ChrisChrisLoLo/bunchiez40/case/experimental_junk/case.stl

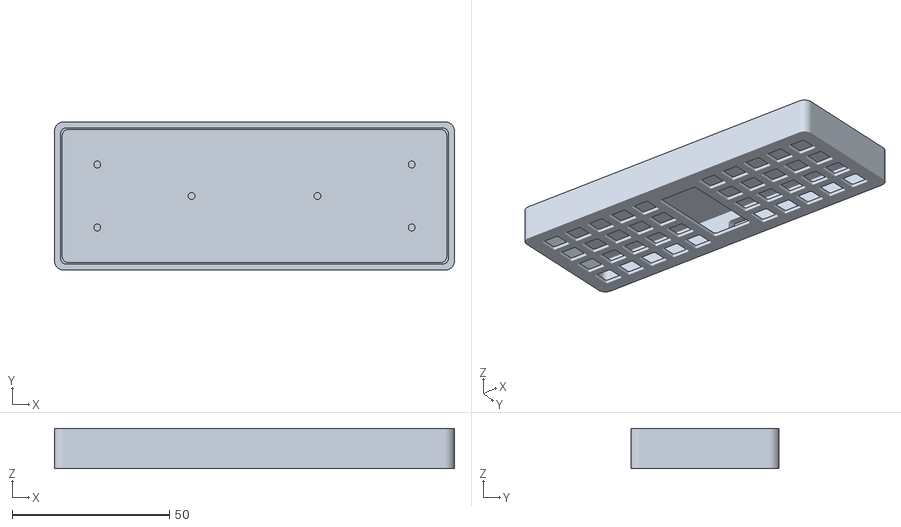
[picture p18: CAD file, 2023-10-13]
case/experimental_junk/case.stl
127.2 x 47.2 x 12.8
