ChrisChrisLoLo/bunchiez40/case/experimental_junk/keycaps.stl

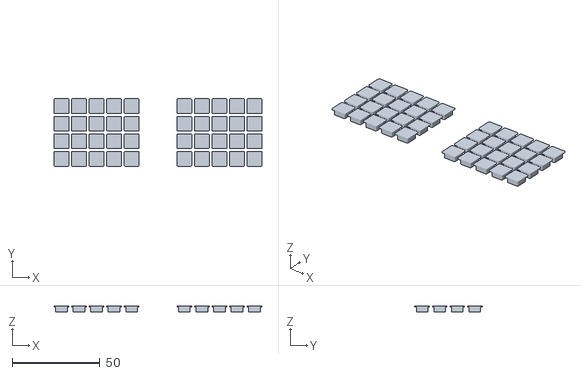
[picture p19: CAD file, 2023-10-13]
case/experimental_junk/keycaps.stl
118.5 x 38.5 x 3.50
