ChrisChrisLoLo/bunchiez40/case/experimental_junk/case_v2.stl

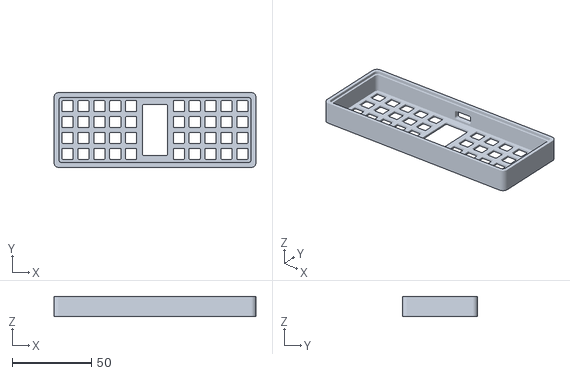
[picture p20: CAD file, 2023-10-13]
case/experimental_junk/case_v2.stl
127.2 x 47.2 x 12.8
